ptravnik/Retro_CALC/HWKbd/src/Cyrillic_Phonetic_CP1251.h

/*
  Cyrillic_Phonetic_CP1251.h - codes and macros for Hardware keyboard.
  Copyright (c) 2019 Pavel Travnik.  All rights reserved.

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
  You should have received a copy of the GNU Lesser General Public
  License along with this library; if not, write to the Free Software
  Foundation, Inc., 51 Franklin St, Fifth Floor, Boston, MA  02110-1301  USA
*/
const static uint16_t HWKBD_Codepage_Cyrillic_Phonetic_CP1251[] PROGMEM = {
  0x001b, 0x001b, 0x2009, 0x3009, 0x401b, 0x401b, 0x6009, 0x7009, // Button 01
  0x8000, 0x002b, 0x8003, 0x8009, 0x40fd, 0x40dd, 0xc00f, 0x402b, // Button 02
  0x8015, 0x002d, 0x8018, 0x002d, 0x40fe, 0x40de, 0xc01e, 0x402d, // Button 03
  0x8024, 0x002a, 0x8027, 0x002a, 0x40fa, 0x40da, 0xc02e, 0x402a, // Button 04
  0x8035, 0x002f, 0x8038, 0x803f, 0x40fc, 0x40dc, 0xc045, 0x402f, // Button 05
  0x804c, 0x005e, 0x005e, 0x804f, 0x40b8, 0x40a8, 0x405e, 0x405e, // Button 06
  0x8056, 0x007e, 0x005c, 0x8059, 0x407e, 0x405c, 0x40b1, 0x40b1, // Button 07
  0x0065, 0x0065, 0x0065, 0x0065, 0x40f8, 0x40d8, 0x4065, 0x4065, // Button 08
  0x002e, 0x002c, 0x003a, 0x003b, 0x40f9, 0x40d9, 0x40b0, 0x403b, // Button 09
  0x805f, 0x8065, 0x806c, 0xb074, 0xc07b, 0xc081, 0xc088, 0xf090, // Button 10
  0x0031, 0x0021, 0x0000, 0x0000, 0x4031, 0x4021, 0x4000, 0x4000, // Button 11
  0x0032, 0x0040, 0x0000, 0x0000, 0x4032, 0x4040, 0x4000, 0x4000, // Button 12
  0x0033, 0x0023, 0x0000, 0x0000, 0x4033, 0x4023, 0x4000, 0x4000, // Button 13
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
  0x32, 0x0d, 0x00, 0x0a, 0x72, 0x61, 0x64, 0x69,
  0x75, 0x73, 0x0d, 0x00, 0x0a, 0x63, 0x61, 0x74,
  0x68, 0x0d, 0x00, 0x0a, 0x72, 0x61, 0x64, 0x69,
  0x75, 0x73, 0x0d, 0x00, 0x0a, 0x63, 0x61, 0x74,
  0x68, 0x0d, 0x00, 0x0a, 0x63, 0x6c, 0x65, 0x61,
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
};
