ptravnik/Retro_CALC/RetroRPN_ESP32/src/Keywords.cpp

//////////////////////////////////////////////////////////
//
//  RetroRPN - "Электроника МК-90" reborn
//  Copyright (c) 2019 Pavel Travnik.  All rights reserved.
//  See main file for the license
//
//////////////////////////////////////////////////////////

#include "Keywords.hpp"

//#define __DEBUG

//#define _OPR_ABS_KW             0
const char _OPR_ABS[] PROGMEM = "ABS";
const char _OPR_abs[] PROGMEM = "abs";
//#define _OPR_ACOS_KW            1
const char _OPR_ACOS[] PROGMEM = "ACOS";
const char _OPR_acos[] PROGMEM = "acos";
//#define _OPR_ACOSH_KW           2
const char _OPR_ACOSH[] PROGMEM = "ACOSH";
const char _OPR_acosh[] PROGMEM = "acosh";
//#define _OPR_ADD_KW             3
const char _OPR_ADD[] PROGMEM = "ADD";
const char _OPR_add[] PROGMEM = "add";
//#define _OPR_AMODE_KW           4
const char _OPR_AMODE[] PROGMEM = "AMODE";
const char _OPR_amode[] PROGMEM = "amode";
//#define _OPR_API2GCC_KW         5
const char _OPR_API2GCC[] PROGMEM = "API2GCC";
const char _OPR_api2gcc[] PROGMEM = "api2gcc";
//#define _OPR_APPEND_KW          6
const char _OPR_APPEND[] PROGMEM = "APPEND";
const char _OPR_append[] PROGMEM = "append";
//#define _OPR_AREAD_KW           7
const char _OPR_AREAD[] PROGMEM = "AREAD";
const char _OPR_aread[] PROGMEM = "aread";
//#define _OPR_AREAD_INT_KW       8
const char _OPR_AREAD_INT[] PROGMEM = "AREAD%";
const char _OPR_aread_INT[] PROGMEM = "aread%";
//#define _OPR_ASC_KW             9
const char _OPR_ASC[] PROGMEM = "ASC";
const char _OPR_asc[] PROGMEM = "asc";
//#define _OPR_ASIN_KW            10
const char _OPR_ASIN[] PROGMEM = "ASIN";
const char _OPR_asin[] PROGMEM = "asin";
//#define _OPR_ASINH_KW           11
const char _OPR_ASINH[] PROGMEM = "ASINH";
const char _OPR_asinh[] PROGMEM = "asinh";
//#define _OPR_AT_KW              12
const char _OPR_AT[] PROGMEM = "AT";
const char _OPR_at[] PROGMEM = "at";
//#define _OPR_ATAN_KW            13
const char _OPR_ATAN[] PROGMEM = "ATAN";
const char _OPR_atan[] PROGMEM = "atan";
//#define _OPR_ATANH_KW           14
const char _OPR_ATANH[] PROGMEM = "ATANH";
const char _OPR_atanh[] PROGMEM = "atanh";
//#define _OPR_AWRITE_KW          15
const char _OPR_AWRITE[] PROGMEM = "AWRITE";
const char _OPR_awrite[] PROGMEM = "awrite";
//#define _OPR_AZIMUTH_KW         16
const char _OPR_AZIMUTH[] PROGMEM = "AZIMUTH";
const char _OPR_azimuth[] PROGMEM = "azimuth";
//#define _OPR_AZIMUTH3_KW        17
const char _OPR_AZIMUTH3[] PROGMEM = "AZIMUTH3";
const char _OPR_azimuth3[] PROGMEM = "azimuth3";
//#define _OPR_BAR2PSI_KW         18
const char _OPR_BAR2PSI[] PROGMEM = "BAR2PSI";
const char _OPR_bar2psi[] PROGMEM = "bar2psi";
//#define _OPR_BBL2CM_KW          19
const char _OPR_BBL2CM[] PROGMEM = "BBL2CM";
const char _OPR_bbl2cm[] PROGMEM = "bbl2cm";
//#define _OPR_BREAK_KW           20
const char _OPR_BREAK[] PROGMEM = "BREAK";
const char _OPR_break[] PROGMEM = "break";
//#define _OPR_C2F_KW             21
const char _OPR_C2F[] PROGMEM = "C2F";
const char _OPR_c2f[] PROGMEM = "c2f";
//#define _OPR_C2K_KW             22
const char _OPR_C2K[] PROGMEM = "C2K";
const char _OPR_c2k[] PROGMEM = "c2k";
//#define _OPR_CATH_KW            23
const char _OPR_CATH[] PROGMEM = "CATH";
const char _OPR_cath[] PROGMEM = "cath";
//#define _OPR_CF2CM_KW           24
const char _OPR_CF2CM[] PROGMEM = "CF2CM";
const char _OPR_cf2cm[] PROGMEM = "cf2cm";
//#define _OPR_CHAIN_KW           25
const char _OPR_CHAIN[] PROGMEM = "CHAIN";
const char _OPR_chain[] PROGMEM = "chain";
//#define _OPR_CHR_STR_KW         26
const char _OPR_CHR_STR[] PROGMEM = "CHR$";
const char _OPR_chr_STR[] PROGMEM = "chr$";
//#define _OPR_CIRCLE_KW          27
const char _OPR_CIRCLE[] PROGMEM = "CIRCLE";
const char _OPR_circle[] PROGMEM = "circle";
//#define _OPR_CLEAR_KW           28
const char _OPR_CLEAR[] PROGMEM = "CLEAR";
const char _OPR_clear[] PROGMEM = "clear";
//#define _OPR_CLI_KW             29
const char _OPR_CLI[] PROGMEM = "CLI";
const char _OPR_cli[] PROGMEM = "cli";
//#define _OPR_CLOSE_KW           30
const char _OPR_CLOSE[] PROGMEM = "CLOSE";
const char _OPR_close[] PROGMEM = "close";
//#define _OPR_CLS_KW             31
const char _OPR_CLS[] PROGMEM = "CLS";
const char _OPR_cls[] PROGMEM = "cls";
//#define _OPR_CM2BBL_KW          32
const char _OPR_CM2BBL[] PROGMEM = "CM2BBL";
const char _OPR_cm2bbl[] PROGMEM = "cm2bbl";
//#define _OPR_CM2CF_KW           33
const char _OPR_CM2CF[] PROGMEM = "CM2CF";
const char _OPR_cm2cf[] PROGMEM = "cm2cf";
//#define _OPR_COLOR_KW           34
const char _OPR_COLOR[] PROGMEM = "COLOR";
const char _OPR_color[] PROGMEM = "color";
//#define _OPR_CON_KW             35
const char _OPR_CON[] PROGMEM = "CON";
const char _OPR_con[] PROGMEM = "con";
//#define _OPR_CONST_KW           36
const char _OPR_CONST[] PROGMEM = "CONST";
const char _OPR_const[] PROGMEM = "const";
//#define _OPR_CONT_KW            37
const char _OPR_CONT[] PROGMEM = "CONT";
const char _OPR_cont[] PROGMEM = "cont";
//#define _OPR_CONTINUE_KW        38
const char _OPR_CONTINUE[] PROGMEM = "CONTINUE";
const char _OPR_continue[] PROGMEM = "continue";
//#define _OPR_COORDS_KW          39
const char _OPR_COORDS[] PROGMEM = "COORDS";
const char _OPR_coords[] PROGMEM = "coords";
//#define _OPR_COORDS3_KW         40
const char _OPR_COORDS3[] PROGMEM = "COORDS3";
const char _OPR_coords3[] PROGMEM = "coords3";
//#define _OPR_COS_KW             41
const char _OPR_COS[] PROGMEM = "COS";
const char _OPR_cos[] PROGMEM = "cos";
//#define _OPR_COSH_KW            42
const char _OPR_COSH[] PROGMEM = "COSH";
const char _OPR_cosh[] PROGMEM = "cosh";
//#define _OPR_COT_KW             43
const char _OPR_COT[] PROGMEM = "COT";
const char _OPR_cot[] PROGMEM = "cot";
//#define _OPR_CURSOR_KW          44
const char _OPR_CURSOR[] PROGMEM = "CURSOR";
const char _OPR_cursor[] PROGMEM = "cursor";
//#define _OPR_D2DMS_KW           45
const char _OPR_D2DMS[] PROGMEM = "D2DMS";
const char _OPR_d2dms[] PROGMEM = "d2dms";
//#define _OPR_DATA_KW            46
const char _OPR_DATA[] PROGMEM = "DATA";
const char _OPR_data[] PROGMEM = "data";
//#define _OPR_DEF_KW             47
const char _OPR_DEF[] PROGMEM = "DEF";
const char _OPR_def[] PROGMEM = "def";
//#define _OPR_DELAY_KW           48
const char _OPR_DELAY[] PROGMEM = "DELAY";
const char _OPR_delay[] PROGMEM = "delay";
//#define _OPR_DET_KW             49
const char _OPR_DET[] PROGMEM = "DET";
const char _OPR_det[] PROGMEM = "det";
//#define _OPR_DIM_KW             50
const char _OPR_DIM[] PROGMEM = "DIM";
const char _OPR_dim[] PROGMEM = "dim";
//#define _OPR_DIR_KW             51
const char _OPR_DIR[] PROGMEM = "DIR";
const char _OPR_dir[] PROGMEM = "dir";
//#define _OPR_DIRECTORY_KW       52
const char _OPR_DIRECTORY[] PROGMEM = "CD";
const char _OPR_directory[] PROGMEM = "cd";
//#define _OPR_DIV_KW             53
const char _OPR_DIV[] PROGMEM = "DIV";
const char _OPR_div[] PROGMEM = "div";
//#define _OPR_DMODE_KW           54
const char _OPR_DMODE[] PROGMEM = "DMODE";
const char _OPR_dmode[] PROGMEM = "dmode";
//#define _OPR_DMS2D_KW           55
const char _OPR_DMS2D[] PROGMEM = "DMS2D";
const char _OPR_dms2d[] PROGMEM = "dms2d";
//#define _OPR_DNOTONE_KW         56
const char _OPR_DNOTONE[] PROGMEM = "DNOTONE";
const char _OPR_dnotone[] PROGMEM = "dnotone";
//#define _OPR_DOT_KW             57
const char _OPR_DOT[] PROGMEM = "DOT";
const char _OPR_dot[] PROGMEM = "dot";
//#define _OPR_DREAD_KW           58
const char _OPR_DREAD[] PROGMEM = "DREAD";
const char _OPR_dread[] PROGMEM = "dread";
//#define _OPR_DTONE_KW           59
const char _OPR_DTONE[] PROGMEM = "DTONE";
const char _OPR_dtone[] PROGMEM = "dtone";
//#define _OPR_DUMP_KW            60
const char _OPR_DUMP[] PROGMEM = "DUMP";
const char _OPR_dump[] PROGMEM = "dump";
//#define _OPR_DWRITE_KW          61
const char _OPR_DWRITE[] PROGMEM = "DWRITE";
const char _OPR_dwrite[] PROGMEM = "dwrite";
//#define _OPR_EDIT_KW            62
const char _OPR_EDIT[] PROGMEM = "EDIT";
const char _OPR_edit[] PROGMEM = "edit";
//#define _OPR_ELLIPSE_KW         63
const char _OPR_ELLIPSE[] PROGMEM = "ELLIPSE";
const char _OPR_ellipse[] PROGMEM = "ellipse";
//#define _OPR_ELSE_KW            64
const char _OPR_ELSE[] PROGMEM = "ELSE";
const char _OPR_else[] PROGMEM = "else";
//#define _OPR_END_KW             65
const char _OPR_END[] PROGMEM = "END";
const char _OPR_end[] PROGMEM = "end";
//#define _OPR_ENDIF_KW           66
const char _OPR_ENDIF[] PROGMEM = "ENDIF";
const char _OPR_endif[] PROGMEM = "endif";
//#define _OPR_ENDLOOP_KW         67
const char _OPR_ENDLOOP[] PROGMEM = "ENDLOOP";
const char _OPR_endloop[] PROGMEM = "endloop";
//#define _OPR_EXP_KW             68
const char _OPR_EXP[] PROGMEM = "EXP";
const char _OPR_exp[] PROGMEM = "exp";
//#define _OPR_F2C_KW             69
const char _OPR_F2C[] PROGMEM = "F2C";
const char _OPR_f2c[] PROGMEM = "f2c";
//#define _OPR_FLOAT_KW           70
const char _OPR_FLOAT[] PROGMEM = "FLOAT";
const char _OPR_float[] PROGMEM = "float";
//#define _OPR_FMAN_KW            71
const char _OPR_FMAN[] PROGMEM = "FMAN";
const char _OPR_fman[] PROGMEM = "fman";
//#define _OPR_FN_KW              72
const char _OPR_FN[] PROGMEM = "FN";
const char _OPR_fn[] PROGMEM = "fn";
//#define _OPR_FOR_KW             73
const char _OPR_FOR[] PROGMEM = "FOR";
const char _OPR_for[] PROGMEM = "for";
//#define _OPR_FREAD_KW           74
const char _OPR_FREAD[] PROGMEM = "FREAD";
const char _OPR_fread[] PROGMEM = "fread";
//#define _OPR_FREAD_STR_KW       75
const char _OPR_FREAD_STR[] PROGMEM = "FREAD$";
const char _OPR_fread_STR[] PROGMEM = "fread$";
//#define _OPR_FSIZE_KW           76
const char _OPR_FSIZE[] PROGMEM = "FSIZE";
const char _OPR_fsize[] PROGMEM = "fsize";
//#define _OPR_FT2M_KW            77
const char _OPR_FT2M[] PROGMEM = "FT2M";
const char _OPR_ft2m[] PROGMEM = "ft2m";
//#define _OPR_GAL2L_KW           78
const char _OPR_GAL2L[] PROGMEM = "GAL2L";
const char _OPR_gal2l[] PROGMEM = "gal2l";
//#define _OPR_GCC2API_KW         79
const char _OPR_GCC2API[] PROGMEM = "GCC2API";
const char _OPR_gcc2api[] PROGMEM = "gcc2api";
//#define _OPR_GOFF2_KW           80
const char _OPR_GOFF2[] PROGMEM = "GOFF2";
const char _OPR_goff2[] PROGMEM = "goff2";
//#define _OPR_GOSUB_KW           81
const char _OPR_GOSUB[] PROGMEM = "GOSUB";
const char _OPR_gosub[] PROGMEM = "gosub";
//#define _OPR_GOTO_KW            82
const char _OPR_GOTO[] PROGMEM = "GOTO";
const char _OPR_goto[] PROGMEM = "goto";
//#define _OPR_HEX_STR_KW         83
const char _OPR_HEX_STR[] PROGMEM = "HEX$";
const char _OPR_hex_STR[] PROGMEM = "hex$";
//#define _OPR_IDN_KW             84
const char _OPR_IDN[] PROGMEM = "IDN";
const char _OPR_idn[] PROGMEM = "idn";
//#define _OPR_IF_KW              85
const char _OPR_IF[] PROGMEM = "IF";
const char _OPR_if[] PROGMEM = "if";
//#define _OPR_INCH16_STR_KW      86
const char _OPR_INCH16_STR[] PROGMEM = "INCH16$";
const char _OPR_inch16_STR[] PROGMEM = "inch16$";
//#define _OPR_INCH2_STR_KW       87
const char _OPR_INCH2_STR[] PROGMEM = "INCH2$";
const char _OPR_inch2_STR[] PROGMEM = "inch2$";
//#define _OPR_INCH32_STR_KW      88
const char _OPR_INCH32_STR[] PROGMEM = "INCH32$";
const char _OPR_inch32_STR[] PROGMEM = "inch32$";
//#define _OPR_INCH32_STR_KW      89
const char _OPR_INCH64_STR[] PROGMEM = "INCH64$";
const char _OPR_inch64_STR[] PROGMEM = "inch64$";
//#define _OPR_INCH4_STR_KW       90
const char _OPR_INCH4_STR[] PROGMEM = "INCH4$";
const char _OPR_inch4_STR[] PROGMEM = "inch4$";
//#define _OPR_INCH8_STR_KW       91
const char _OPR_INCH8_STR[] PROGMEM = "INCH8$";
const char _OPR_inch8_STR[] PROGMEM = "inch8$";
//#define _OPR_INJ_KW             92
const char _OPR_INJ[] PROGMEM = "INJ";
const char _OPR_inj[] PROGMEM = "inj";
//#define _OPR_INKEY_STR_KW       93
const char _OPR_INKEY_STR[] PROGMEM = "INKEY$";
const char _OPR_inkey_STR[] PROGMEM = "inkey$";
//#define _OPR_INPUT_KW           94
const char _OPR_INPUT[] PROGMEM = "INPUT";
const char _OPR_input[] PROGMEM = "input";
//#define _OPR_INSCAN_STR_KW      95
const char _OPR_INSCAN_STR[] PROGMEM = "INSCAN$";
const char _OPR_inscan_STR[] PROGMEM = "inscan$";
//#define _OPR_INT_INT_KW         96
const char _OPR_INT_INT[] PROGMEM = "INT%";
const char _OPR_int_INT[] PROGMEM = "int%";
//#define _OPR_INV_KW             97
const char _OPR_INV[] PROGMEM = "INV";
const char _OPR_inv[] PROGMEM = "inv";
//#define _OPR_KG2LBS_KW          98
const char _OPR_KG2LBS[] PROGMEM = "KG2LBS";
const char _OPR_kg2lbs[] PROGMEM = "kg2lbs";
//#define _OPR_KM2M_KW            99
const char _OPR_KM2M[] PROGMEM = "KM2M";
const char _OPR_km2m[] PROGMEM = "km2m";
//#define _OPR_KM2NM_KW           100
const char _OPR_KM2NM[] PROGMEM = "KM2NM";
const char _OPR_km2nm[] PROGMEM = "km2nm";
//#define _OPR_KMH2MS_KW          101
const char _OPR_KMH2MS[] PROGMEM = "KMH2MS";
const char _OPR_kmh2ms[] PROGMEM = "kmh2ms";
//#define _OPR_L2GAL_KW           102
const char _OPR_L2GAL[] PROGMEM = "L2GAL";
const char _OPR_l2gal[] PROGMEM = "l2gal";
//#define _OPR_LBS2KG_KW          103
const char _OPR_LBS2KG[] PROGMEM = "LBS2KG";
const char _OPR_lbs2kg[] PROGMEM = "lbs2kg";
//#define _OPR_LCIRC_KW           104
const char _OPR_LCIRC[] PROGMEM = "LCIRC";
const char _OPR_lcirc[] PROGMEM = "lcirc";
//#define _OPR_LEFT_STR_KW        105
const char _OPR_LEFT_STR[] PROGMEM = "LEFT$";
const char _OPR_left_STR[] PROGMEM = "left$";
//#define _OPR_LET_KW             106
const char _OPR_LET[] PROGMEM = "LET";
const char _OPR_let[] PROGMEM = "let";
//#define _OPR_LG_KW              107
const char _OPR_LG[] PROGMEM = "LG";
const char _OPR_lg[] PROGMEM = "lg";
//#define _OPR_LIN2_KW            108
const char _OPR_LIN2[] PROGMEM = "LIN2";
const char _OPR_lin2[] PROGMEM = "lin2";
//#define _OPR_LINE_KW            109
const char _OPR_LINE[] PROGMEM = "LINE";
const char _OPR_line[] PROGMEM = "line";
//#define _OPR_LINETO_KW          110
const char _OPR_LINETO[] PROGMEM = "LINETO";
const char _OPR_lineto[] PROGMEM = "lineto";
//#define _OPR_LINEW_KW           111
const char _OPR_LINEW[] PROGMEM = "LINEW";
const char _OPR_linew[] PROGMEM = "linew";
//#define _OPR_LIST_KW            112
const char _OPR_LIST[] PROGMEM = "LIST";
const char _OPR_list[] PROGMEM = "list";
//#define _OPR_LN_KW              113
const char _OPR_LN[] PROGMEM = "LN";
const char _OPR_ln[] PROGMEM = "ln";
//#define _OPR_LOAD_KW            114
const char _OPR_LOAD[] PROGMEM = "LOAD";
const char _OPR_load[] PROGMEM = "load";
//#define _OPR_LOG_KW             115
const char _OPR_LOG[] PROGMEM = "LOG";
const char _OPR_log[] PROGMEM = "log";
//#define _OPR_LOOP_KW            116
const char _OPR_LOOP[] PROGMEM = "LOOP";
const char _OPR_loop[] PROGMEM = "loop";
//#define _OPR_LT2MT_KW           117
const char _OPR_LT2MT[] PROGMEM = "LT2MT";
const char _OPR_lt2mt[] PROGMEM = "lt2mt";
//#define _OPR_M2FT_KW            118
const char _OPR_M2FT[] PROGMEM = "M2FT";
const char _OPR_m2ft[] PROGMEM = "m2ft";
//#define _OPR_M2KM_KW            119
const char _OPR_M2KM[] PROGMEM = "M2KM";
const char _OPR_m2km[] PROGMEM = "m2km";
//#define _OPR_MAT_KW             120
const char _OPR_MAT[] PROGMEM = "MAT";
const char _OPR_mat[] PROGMEM = "mat";
//#define _OPR_MATRIX_KW          121
const char _OPR_MATRIX[] PROGMEM = "MATRIX";
const char _OPR_matrix[] PROGMEM = "matrix";
//#define _OPR_MEM_KW             122
const char _OPR_MEM[] PROGMEM = "MEM";
const char _OPR_mem[] PROGMEM = "mem";
//#define _OPR_MID_STR_KW         123
const char _OPR_MID_STR[] PROGMEM = "MID$";
const char _OPR_mid_STR[] PROGMEM = "mid$";
//#define _OPR_MM2IN_KW           124
const char _OPR_MM2IN[] PROGMEM = "MM2IN";
const char _OPR_mm2in[] PROGMEM = "mm2in";
//#define _OPR_MOD_KW             125
const char _OPR_MOD[] PROGMEM = "MOD";
const char _OPR_mod[] PROGMEM = "mod";
//#define _OPR_MPA2PSI_KW         126
const char _OPR_MPA2PSI[] PROGMEM = "MPA2PSI";
const char _OPR_mpa2psi[] PROGMEM = "mpa2psi";
//#define _OPR_MS2KMH_KW          127
const char _OPR_MS2KMH[] PROGMEM = "MS2KMH";
const char _OPR_ms2kmh[] PROGMEM = "ms2kmh";
//#define _OPR_MT2LT_KW           128
const char _OPR_MT2LT[] PROGMEM = "MT2LT";
const char _OPR_mt2lt[] PROGMEM = "mt2lt";
//#define _OPR_MT2ST_KW           129
const char _OPR_MT2ST[] PROGMEM = "MT2ST";
const char _OPR_mt2st[] PROGMEM = "mt2st";
//#define _OPR_MUL_KW             130
const char _OPR_MUL[] PROGMEM = "MUL";
const char _OPR_mul[] PROGMEM = "mul";
//#define _OPR_NDIS_KW            131
const char _OPR_NDIS[] PROGMEM = "NDIS";
const char _OPR_ndis[] PROGMEM = "ndis";
//#define _OPR_NEG_KW             132
const char _OPR_NEG[] PROGMEM = "NEG";
const char _OPR_neg[] PROGMEM = "neg";
//#define _OPR_NEW_KW             133
const char _OPR_NEW[] PROGMEM = "NEW";
const char _OPR_new[] PROGMEM = "new";
//#define _OPR_NEXT_KW            134
const char _OPR_NEXT[] PROGMEM = "NEXT";
const char _OPR_next[] PROGMEM = "next";
//#define _OPR_NM2KM_KW           135
const char _OPR_NM2KM[] PROGMEM = "NM2KM";
const char _OPR_nm2km[] PROGMEM = "nm2km";
//#define _OPR_OPEN_KW            136
const char _OPR_OPEN[] PROGMEM = "OPEN";
const char _OPR_open[] PROGMEM = "open";
//#define _OPR_PA2PSI_KW          137
const char _OPR_PA2PSI[] PROGMEM = "PA2PSI";
const char _OPR_pa2psi[] PROGMEM = "pa2psi";
//#define _OPR_PAUSE_KW           138
const char _OPR_PAUSE[] PROGMEM = "PAUSE";
const char _OPR_pause[] PROGMEM = "pause";
//#define _OPR_POINT_KW           139
const char _OPR_POINT[] PROGMEM = "POINT";
const char _OPR_point[] PROGMEM = "point";
//#define _OPR_POKE_KW            140
const char _OPR_POKE[] PROGMEM = "POKE";
const char _OPR_poke[] PROGMEM = "poke";
//#define _OPR_POP_KW             141
const char _OPR_POP[] PROGMEM = "POP";
const char _OPR_pop[] PROGMEM = "pop";
//#define _OPR_POW_KW             142
const char _OPR_POW[] PROGMEM = "POW";
const char _OPR_pow[] PROGMEM = "pow";
//#define _OPR_PRINT_KW           143
const char _OPR_PRINT[] PROGMEM = "PRINT";
const char _OPR_print[] PROGMEM = "print";
//#define _OPR_PRINTALT_KW        144
const char _OPR_PRINTALT[] PROGMEM = "?";
const char _OPR_printalt[] PROGMEM = "?";
//#define _OPR_PROB_KW            145
const char _OPR_PROB[] PROGMEM = "PROB";
const char _OPR_prob[] PROGMEM = "prob";
//#define _OPR_PROBIT_KW          146
const char _OPR_PROBIT[] PROGMEM = "PROBIT";
const char _OPR_probit[] PROGMEM = "probit";
//#define _OPR_PROBR_KW           147
const char _OPR_PROBR[] PROGMEM = "PROBR";
const char _OPR_probr[] PROGMEM = "probr";
//#define _OPR_PROGRAM_KW         148
const char _OPR_PROGRAM[] PROGMEM = "PROGRAM";
const char _OPR_program[] PROGMEM = "program";
//#define _OPR_PSI2BAR_KW         149
const char _OPR_PSI2BAR[] PROGMEM = "PSI2BAR";
const char _OPR_psi2bar[] PROGMEM = "psi2bar";
//#define _OPR_PSI2MPA_KW         150
const char _OPR_PSI2MPA[] PROGMEM = "PSI2MPA";
const char _OPR_psi2mpa[] PROGMEM = "psi2mpa";
//#define _OPR_PSI2PA_KW          151
const char _OPR_PSI2PA[] PROGMEM = "PSI2PA";
const char _OPR_psi2pa[] PROGMEM = "psi2pa";
//#define _OPR_PSIA2PSIG_KW       152
const char _OPR_PSIA2PSIG[] PROGMEM = "PSIA2PSIG";
const char _OPR_psia2psig[] PROGMEM = "psia2psig";
//#define _OPR_PSIG2PSIA_KW       153
const char _OPR_PSIG2PSIA[] PROGMEM = "PSIG2PSIA";
const char _OPR_psig2psia[] PROGMEM = "psig2psia";
//#define _OPR_PUSH_KW            154
const char _OPR_PUSH[] PROGMEM = "PUSH";
const char _OPR_push[] PROGMEM = "push";
//#define _OPR_QUAD_KW            155
const char _OPR_QUAD[] PROGMEM = "QUAD";
const char _OPR_quad[] PROGMEM = "quad";
//#define _OPR_RADIUS_KW          156
const char _OPR_RADIUS[] PROGMEM = "RADIUS";
const char _OPR_radius[] PROGMEM = "radius";
//#define _OPR_RANDOM_KW          157
const char _OPR_RANDOM[] PROGMEM = "RANDOM";
const char _OPR_random[] PROGMEM = "random";
//#define _OPR_RANDOM_INT_KW      158
const char _OPR_RANDOM_INT[] PROGMEM = "RANDOM%";
const char _OPR_random_INT[] PROGMEM = "random%";
//#define _OPR_READ_KW            159
const char _OPR_READ[] PROGMEM = "READ";
const char _OPR_read[] PROGMEM = "read";
//#define _OPR_RECT_KW            160
const char _OPR_RECT[] PROGMEM = "RECT";
const char _OPR_rect[] PROGMEM = "rect";
//#define _OPR_REGR_KW            161
const char _OPR_REGR[] PROGMEM = "REGR";
const char _OPR_regr[] PROGMEM = "regr";
//#define _OPR_REM_KW             162
const char _OPR_REM[] PROGMEM = "REM";
const char _OPR_rem[] PROGMEM = "rem";
//#define _OPR_REMALT_KW          163
const char _OPR_REMALT[] PROGMEM = "#";
const char _OPR_remalt[] PROGMEM = "#";
//#define _OPR_RESET_KW           164
const char _OPR_RESET[] PROGMEM = "RESET";
const char _OPR_reset[] PROGMEM = "reset";
//#define _OPR_RESTORE_KW         165
const char _OPR_RESTORE[] PROGMEM = "RESTORE";
const char _OPR_restore[] PROGMEM = "restore";
//#define _OPR_RIGHT_STR_KW       166
const char _OPR_RIGHT_STR[] PROGMEM = "RIGHT$";
const char _OPR_right_STR[] PROGMEM = "right$";
//#define _OPR_RMD_KW             167
const char _OPR_RMD[] PROGMEM = "RMD";
const char _OPR_rmd[] PROGMEM = "rmd";
//#define _OPR_RND_KW             168
const char _OPR_RND[] PROGMEM = "RND";
const char _OPR_rnd[] PROGMEM = "rnd";
//#define _OPR_ROOT_KW            169
const char _OPR_ROOT[] PROGMEM = "ROOT";
const char _OPR_root[] PROGMEM = "root";
//#define _OPR_ROT_KW             170
const char _OPR_ROT[] PROGMEM = "ROT";
const char _OPR_rot[] PROGMEM = "rot";
//#define _OPR_ROT3c_KW           171
const char _OPR_ROT3c[] PROGMEM = "ROT3c";
const char _OPR_rot3c[] PROGMEM = "rot3c";
//#define _OPR_ROT3s_KW           172
const char _OPR_ROT3s[] PROGMEM = "ROT3s";
const char _OPR_rot3s[] PROGMEM = "rot3s";
//#define _OPR_ROUND_KW           173
const char _OPR_ROUND[] PROGMEM = "ROUND";
const char _OPR_round[] PROGMEM = "round";
//#define _OPR_RPN_KW             174
const char _OPR_RPN[] PROGMEM = "RPN";
const char _OPR_rpn[] PROGMEM = "rpn";
//#define _OPR_RUN_KW             175
const char _OPR_RUN[] PROGMEM = "RUN";
const char _OPR_run[] PROGMEM = "run";
//#define _OPR_SAVE_KW            176
const char _OPR_SAVE[] PROGMEM = "SAVE";
const char _OPR_save[] PROGMEM = "save";
//#define _OPR_SCIRC_KW           177
const char _OPR_SCIRC[] PROGMEM = "SCIRC";
const char _OPR_scirc[] PROGMEM = "scirc";
//#define _OPR_SCREEN_KW          178
const char _OPR_SCREEN[] PROGMEM = "SCREEN";
const char _OPR_screen[] PROGMEM = "screen";
//#define _OPR_SEED_KW            179
const char _OPR_SEED[] PROGMEM = "SEED";
const char _OPR_seed[] PROGMEM = "seed";
//#define _OPR_SIGN_KW            180
const char _OPR_SIGN[] PROGMEM = "SIGN";
const char _OPR_sign[] PROGMEM = "sign";
//#define _OPR_SIN_KW             181
const char _OPR_SIN[] PROGMEM = "SIN";
const char _OPR_sin[] PROGMEM = "sin";
//#define _OPR_SINH_KW            182
const char _OPR_SINH[] PROGMEM = "SINH";
const char _OPR_sinh[] PROGMEM = "sinh";
//#define _OPR_SM2SFT_KW          183
const char _OPR_SM2SFT[] PROGMEM = "SM2SFT";
const char _OPR_sm2sft[] PROGMEM = "sm2sft";
//#define _OPR_SQ_KW              184
const char _OPR_SQ[] PROGMEM = "SQ";
const char _OPR_sq[] PROGMEM = "sq";
//#define _OPR_SQRT_KW            185
const char _OPR_SQRT[] PROGMEM = "SQRT";
const char _OPR_sqrt[] PROGMEM = "sqrt";
//#define _OPR_SSPHERE_KW         186
const char _OPR_SSPHERE[] PROGMEM = "SSPHERE";
const char _OPR_ssphere[] PROGMEM = "ssphere";
//#define _OPR_ST2MT_KW           187
const char _OPR_ST2MT[] PROGMEM = "ST2MT";
const char _OPR_st2mt[] PROGMEM = "st2mt";
//#define _OPR_STACK_KW           188
const char _OPR_STACK[] PROGMEM = "STACK";
const char _OPR_stack[] PROGMEM = "stack";
//#define _OPR_STAT_KW            189
const char _OPR_STAT[] PROGMEM = "STAT";
const char _OPR_stat[] PROGMEM = "stat";
//#define _OPR_STATXY_KW          190
const char _OPR_STATXY[] PROGMEM = "STATXY";
const char _OPR_statxy[] PROGMEM = "statxy";
//#define _OPR_STEP_KW            191
const char _OPR_STEP[] PROGMEM = "STEP";
const char _OPR_step[] PROGMEM = "step";
//#define _OPR_STOP_KW            192
const char _OPR_STOP[] PROGMEM = "STOP";
const char _OPR_stop[] PROGMEM = "stop";
//#define _OPR_STORE_KW           193
const char _OPR_STORE[] PROGMEM = "STORE";
const char _OPR_store[] PROGMEM = "store";
//#define _OPR_STR_STR_KW         194
const char _OPR_STR_STR[] PROGMEM = "STR$";
const char _OPR_str_STR[] PROGMEM = "str$";
//#define _OPR_SUB_KW             195
const char _OPR_SUB[] PROGMEM = "SUB";
const char _OPR_sub[] PROGMEM = "sub";
//#define _OPR_SUM_KW             196
const char _OPR_SUM[] PROGMEM = "SUM";
const char _OPR_sum[] PROGMEM = "sum";
//#define _OPR_SUMS_KW            197
const char _OPR_SUMS[] PROGMEM = "SUMS";
const char _OPR_sums[] PROGMEM = "sums";
//#define _OPR_SUMXY_KW           198
const char _OPR_SUMXY[] PROGMEM = "SUMXY";
const char _OPR_sumxy[] PROGMEM = "sumxy";
//#define _OPR_SWAP_KW            199
const char _OPR_SWAP[] PROGMEM = "SWAP";
const char _OPR_swap[] PROGMEM = "swap";
//#define _OPR_TAN_KW             200
const char _OPR_TAN[] PROGMEM = "TAN";
const char _OPR_tan[] PROGMEM = "tan";
//#define _OPR_TANH_KW            201
const char _OPR_TANH[] PROGMEM = "TANH";
const char _OPR_tanh[] PROGMEM = "tanh";
//#define _OPR_TERM_KW            202
const char _OPR_TERM[] PROGMEM = "TERM";
const char _OPR_term[] PROGMEM = "term";
//#define _OPR_TIME_KW            203
const char _OPR_TIME[] PROGMEM = "TIME";
const char _OPR_time[] PROGMEM = "time";
//#define _OPR_TO_KW              204
const char _OPR_TO[] PROGMEM = "TO";
const char _OPR_to[] PROGMEM = "to";
//#define _OPR_TRN_KW             205
const char _OPR_TRN[] PROGMEM = "TRN";
const char _OPR_trn[] PROGMEM = "trn";
//#define _OPR_VARS_KW            206
const char _OPR_VARS[] PROGMEM = "VARS";
const char _OPR_vars[] PROGMEM = "vars";
//#define _OPR_VECTOR_KW          207
const char _OPR_VECTOR[] PROGMEM = "VECTOR";
const char _OPR_vector[] PROGMEM = "vector";
//#define _OPR_VSPHERE_KW         208
const char _OPR_VSPHERE[] PROGMEM = "VSPHERE";
const char _OPR_vsphere[] PROGMEM = "vsphere";
//#define _OPR_WEEKDAY_KW         209
const char _OPR_WEEKDAY[] PROGMEM = "WEEKDAY";
const char _OPR_weekday[] PROGMEM = "weekday";
//#define _OPR_WRITE_KW           210
const char _OPR_WRITE[] PROGMEM = "WRITE";
const char _OPR_write[] PROGMEM = "write";
//#define _OPR_ZER_KW             211
const char _OPR_ZER[] PROGMEM = "ZER";
const char _OPR_zer[] PROGMEM = "zer";
//#define _OPR_ROLL_KW            212
const char _OPR_ROLL[] PROGMEM = "ROLL";
const char _OPR_roll[] PROGMEM = "roll";
//#define _OPR_OOX_KW             213
const char _OPR_OOX[] PROGMEM = "OOX";
const char _OPR_oox[] PROGMEM = "oox";
//#define _OPR_FACT_KW             214
const char _OPR_FACT[] PROGMEM = "FACT";
const char _OPR_fact[] PROGMEM = "fact";
//#define _OPR_OOX_KW             215
const char _OPR_CNK[] PROGMEM = "CNK";
const char _OPR_cnk[] PROGMEM = "cnk";
//#define _OPR_K2C_KW             216
const char _OPR_K2C[] PROGMEM = "K2C";
const char _OPR_k2c[] PROGMEM = "k2c";
//#define _OPR_AIN_KW             217
const char _OPR_AIN[] PROGMEM = "AIN";
const char _OPR_ain[] PROGMEM = "ain";
//#define _OPR_KM2MI_KW           218
const char _OPR_KM2MI[] PROGMEM = "KM2MI";
const char _OPR_km2mi[] PROGMEM = "km2mi";
//#define _OPR_MI2KM_KW           219
const char _OPR_MI2KM[] PROGMEM = "KM2MI";
const char _OPR_mi2km[] PROGMEM = "mi2km";
//#define _OPR_IN2MM_KW           220
const char _OPR_IN2MM[] PROGMEM = "IN2MM";
const char _OPR_in2mm[] PROGMEM = "in2mm";
//#define _OPR_SFT2SM_KW          221
const char _OPR_SFT2SM[] PROGMEM = "SFT2SM";
const char _OPR_sft2sm[] PROGMEM = "sft2sm";
//#define _OPR_R2D_KW             222
const char _OPR_R2D[] PROGMEM = "R2D";
const char _OPR_r2d[] PROGMEM = "r2d";
//#define _OPR_D2R_KW             223
const char _OPR_D2R[] PROGMEM = "D2R";
const char _OPR_d2r[] PROGMEM = "d2r";
//#define _OPR_DELETE_KW          224
const char _OPR_DELETE[] PROGMEM = "DELETE";
const char _OPR_delete[] PROGMEM = "delete";
//#define _OPR_MOVE_KW            225
const char _OPR_MOVE[] PROGMEM = "MOVE";
const char _OPR_move[] PROGMEM = "move";
//#define _OPR_COPY_KW            226
const char _OPR_COPY[] PROGMEM = "COPY";
const char _OPR_copy[] PROGMEM = "copy";
//#define _OPR_TYPE_KW            227
const char _OPR_TYPE[] PROGMEM = "TYPE";
const char _OPR_type[] PROGMEM = "type";
//#define _OPR_INJECT_KW          228
const char _OPR_INJECT[] PROGMEM = "INJECT";
const char _OPR_inject[] PROGMEM = "inject";
//#define _OPR_MKDIR_KW           229
const char _OPR_MKDIR[] PROGMEM = "MKDIR";
const char _OPR_mkdir[] PROGMEM = "mkdir";


void Keywords::init(){
  _addKeyword( _OPR_ABS, _OPR_abs);                    // 0
  _addKeyword( _OPR_ACOS, _OPR_acos);                  // 1
  _addKeyword( _OPR_ACOSH, _OPR_acosh);                // 2
  _addKeyword( _OPR_ADD, _OPR_add);                    // 3
  _addKeyword( _OPR_AMODE, _OPR_amode);                // 4
  _addKeyword( _OPR_API2GCC, _OPR_api2gcc);            // 5
  _addKeyword( _OPR_APPEND, _OPR_append);              // 6
  _addKeyword( _OPR_AREAD, _OPR_aread);                // 7
  _addKeyword( _OPR_AREAD_INT, _OPR_aread_INT);        // 8
  _addKeyword( _OPR_ASC, _OPR_asc);                    // 9
  _addKeyword( _OPR_ASIN, _OPR_asin);                  // 10
  _addKeyword( _OPR_ASINH, _OPR_asinh);                // 11
  _addKeyword( _OPR_AT, _OPR_at);                      // 12
  _addKeyword( _OPR_ATAN, _OPR_atan);                  // 13
  _addKeyword( _OPR_ATANH, _OPR_atanh);                // 14
  _addKeyword( _OPR_AWRITE, _OPR_awrite);              // 15
  _addKeyword( _OPR_AZIMUTH, _OPR_azimuth);            // 16
  _addKeyword( _OPR_AZIMUTH3, _OPR_azimuth3);          // 17
  _addKeyword( _OPR_BAR2PSI, _OPR_bar2psi);            // 18
  _addKeyword( _OPR_BBL2CM, _OPR_bbl2cm);              // 19
  _addKeyword( _OPR_BREAK, _OPR_break);                // 20
  _addKeyword( _OPR_C2F, _OPR_c2f);                    // 21
  _addKeyword( _OPR_C2K, _OPR_c2k);                    // 22
  _addKeyword( _OPR_CATH, _OPR_cath);                  // 23
  _addKeyword( _OPR_CF2CM, _OPR_cf2cm);                // 24
  _addKeyword( _OPR_CHAIN, _OPR_chain);                // 25
  _addKeyword( _OPR_CHR_STR, _OPR_chr_STR);            // 26
  _addKeyword( _OPR_CIRCLE, _OPR_circle);              // 27
  _addKeyword( _OPR_CLEAR, _OPR_clear);                // 28
  _addKeyword( _OPR_CLI, _OPR_cli);                    // 29
  _addKeyword( _OPR_CLOSE, _OPR_close);                // 30
  _addKeyword( _OPR_CLS, _OPR_cls);                    // 31
  _addKeyword( _OPR_CM2BBL, _OPR_cm2bbl);              // 32
  _addKeyword( _OPR_CM2CF, _OPR_cm2cf);                // 33
  _addKeyword( _OPR_COLOR, _OPR_color);                // 34
  _addKeyword( _OPR_CON, _OPR_con);                    // 35
  _addKeyword( _OPR_CONST, _OPR_const);                // 36
  _addKeyword( _OPR_CONT, _OPR_cont);                  // 37
  _addKeyword( _OPR_CONTINUE, _OPR_continue);          // 38
  _addKeyword( _OPR_COORDS, _OPR_coords);              // 39
  _addKeyword( _OPR_COORDS3, _OPR_coords3);            // 40
  _addKeyword( _OPR_COS, _OPR_cos);                    // 41
  _addKeyword( _OPR_COSH, _OPR_cosh);                  // 42
  _addKeyword( _OPR_COT, _OPR_cot);                    // 43
  _addKeyword( _OPR_CURSOR, _OPR_cursor);              // 44
  _addKeyword( _OPR_D2DMS, _OPR_d2dms);                // 45
  _addKeyword( _OPR_DATA, _OPR_data);                  // 46
  _addKeyword( _OPR_DEF, _OPR_def);                    // 47
  _addKeyword( _OPR_DELAY, _OPR_delay);                // 48
  _addKeyword( _OPR_DET, _OPR_det);                    // 49
  _addKeyword( _OPR_DIM, _OPR_dim);                    // 50
  _addKeyword( _OPR_DIR, _OPR_dir);                    // 51
  _addKeyword( _OPR_DIRECTORY, _OPR_directory);        // 52
  _addKeyword( _OPR_DIV, _OPR_div);                    // 53
  _addKeyword( _OPR_DMODE, _OPR_dmode);                // 54
  _addKeyword( _OPR_DMS2D, _OPR_dms2d);                // 55
  _addKeyword( _OPR_DNOTONE, _OPR_dnotone);            // 56
  _addKeyword( _OPR_DOT, _OPR_dot);                    // 57
  _addKeyword( _OPR_DREAD, _OPR_dread);                // 58
  _addKeyword( _OPR_DTONE, _OPR_dtone);                // 59
  _addKeyword( _OPR_DUMP, _OPR_dump);                  // 60
  _addKeyword( _OPR_DWRITE, _OPR_dwrite);              // 61
  _addKeyword( _OPR_EDIT, _OPR_edit);                  // 62
  _addKeyword( _OPR_ELLIPSE, _OPR_ellipse);            // 63
  _addKeyword( _OPR_ELSE, _OPR_else);                  // 64
  _addKeyword( _OPR_END, _OPR_end);                    // 65
  _addKeyword( _OPR_ENDIF, _OPR_endif);                // 66
  _addKeyword( _OPR_ENDLOOP, _OPR_endloop);            // 67
  _addKeyword( _OPR_EXP, _OPR_exp);                    // 68
  _addKeyword( _OPR_F2C, _OPR_f2c);                    // 69
  _addKeyword( _OPR_FLOAT, _OPR_float);                // 70
  _addKeyword( _OPR_FMAN, _OPR_fman);                  // 71
  _addKeyword( _OPR_FN, _OPR_fn);                      // 72
  _addKeyword( _OPR_FOR, _OPR_for);                    // 73
  _addKeyword( _OPR_FREAD, _OPR_fread);                // 74
  _addKeyword( _OPR_FREAD_STR, _OPR_fread_STR);        // 75
  _addKeyword( _OPR_FSIZE, _OPR_fsize);                // 76
  _addKeyword( _OPR_FT2M, _OPR_ft2m);                  // 77
  _addKeyword( _OPR_GAL2L, _OPR_gal2l);                // 78
  _addKeyword( _OPR_GCC2API, _OPR_gcc2api);            // 79
  _addKeyword( _OPR_GOFF2, _OPR_goff2);                // 80
  _addKeyword( _OPR_GOSUB, _OPR_gosub);                // 81
  _addKeyword( _OPR_GOTO, _OPR_goto);                  // 82
  _addKeyword( _OPR_HEX_STR, _OPR_hex_STR);            // 83
  _addKeyword( _OPR_IDN, _OPR_idn);                    // 84
  _addKeyword( _OPR_IF, _OPR_if);                      // 85
  _addKeyword( _OPR_INCH16_STR, _OPR_inch16_STR);      // 86
  _addKeyword( _OPR_INCH2_STR, _OPR_inch2_STR);        // 87
  _addKeyword( _OPR_INCH32_STR, _OPR_inch32_STR);      // 88
  _addKeyword( _OPR_INCH32_STR, _OPR_inch32_STR);      // 89
  _addKeyword( _OPR_INCH4_STR, _OPR_inch4_STR);        // 90
  _addKeyword( _OPR_INCH8_STR, _OPR_inch8_STR);        // 91
  _addKeyword( _OPR_INJ, _OPR_inj);                    // 92
  _addKeyword( _OPR_INKEY_STR, _OPR_inkey_STR);        // 93
  _addKeyword( _OPR_INPUT, _OPR_input);                // 94
  _addKeyword( _OPR_INSCAN_STR, _OPR_inscan_STR);      // 95
  _addKeyword( _OPR_INT_INT, _OPR_int_INT);            // 96
  _addKeyword( _OPR_INV, _OPR_inv);                    // 97
  _addKeyword( _OPR_KG2LBS, _OPR_kg2lbs);              // 98
  _addKeyword( _OPR_KM2M, _OPR_km2m);                  // 99
  _addKeyword( _OPR_KM2NM, _OPR_km2nm);                // 100
  _addKeyword( _OPR_KMH2MS, _OPR_kmh2ms);              // 101
  _addKeyword( _OPR_L2GAL, _OPR_l2gal);                // 102
  _addKeyword( _OPR_LBS2KG, _OPR_lbs2kg);              // 103
  _addKeyword( _OPR_LCIRC, _OPR_lcirc);                // 104
  _addKeyword( _OPR_LEFT_STR, _OPR_left_STR);          // 105
  _addKeyword( _OPR_LET, _OPR_let);                    // 106
  _addKeyword( _OPR_LG, _OPR_lg);                      // 107
  _addKeyword( _OPR_LIN2, _OPR_lin2);                  // 108
  _addKeyword( _OPR_LINE, _OPR_line);                  // 109
  _addKeyword( _OPR_LINETO, _OPR_lineto);              // 110
  _addKeyword( _OPR_LINEW, _OPR_linew);                // 111
  _addKeyword( _OPR_LIST, _OPR_list);                  // 112
  _addKeyword( _OPR_LN, _OPR_ln);                      // 113
  _addKeyword( _OPR_LOAD, _OPR_load);                  // 114
  _addKeyword( _OPR_LOG, _OPR_log);                    // 115
  _addKeyword( _OPR_LOOP, _OPR_loop);                  // 116
  _addKeyword( _OPR_LT2MT, _OPR_lt2mt);                // 117
  _addKeyword( _OPR_M2FT, _OPR_m2ft);                  // 118
  _addKeyword( _OPR_M2KM, _OPR_m2km);                  // 119
  _addKeyword( _OPR_MAT, _OPR_mat);                    // 120
  _addKeyword( _OPR_MATRIX, _OPR_matrix);              // 121
  _addKeyword( _OPR_MEM, _OPR_mem);                    // 122
  _addKeyword( _OPR_MID_STR, _OPR_mid_STR);            // 123
  _addKeyword( _OPR_MM2IN, _OPR_mm2in);                // 124
  _addKeyword( _OPR_MOD, _OPR_mod);                    // 125
  _addKeyword( _OPR_MPA2PSI, _OPR_mpa2psi);            // 126
  _addKeyword( _OPR_MS2KMH, _OPR_ms2kmh);              // 127
  _addKeyword( _OPR_MT2LT, _OPR_mt2lt);                // 128
  _addKeyword( _OPR_MT2ST, _OPR_mt2st);                // 129
  _addKeyword( _OPR_MUL, _OPR_mul);                    // 130
  _addKeyword( _OPR_NDIS, _OPR_ndis);                  // 131
  _addKeyword( _OPR_NEG, _OPR_neg);                    // 132
  _addKeyword( _OPR_NEW, _OPR_new);                    // 133
  _addKeyword( _OPR_NEXT, _OPR_next);                  // 134
  _addKeyword( _OPR_NM2KM, _OPR_nm2km);                // 135
  _addKeyword( _OPR_OPEN, _OPR_open);                  // 136
  _addKeyword( _OPR_PA2PSI, _OPR_pa2psi);              // 137
  _addKeyword( _OPR_PAUSE, _OPR_pause);                // 138
  _addKeyword( _OPR_POINT, _OPR_point);                // 139
  _addKeyword( _OPR_POKE, _OPR_poke);                  // 140
  _addKeyword( _OPR_POP, _OPR_pop);                    // 141
  _addKeyword( _OPR_POW, _OPR_pow);                    // 142
  _addKeyword( _OPR_PRINT, _OPR_print);                // 143
  _addKeyword( _OPR_PRINTALT, _OPR_printalt);          // 144
  _addKeyword( _OPR_PROB, _OPR_prob);                  // 145
  _addKeyword( _OPR_PROBIT, _OPR_probit);              // 146
  _addKeyword( _OPR_PROBR, _OPR_probr);                // 147
  _addKeyword( _OPR_PROGRAM, _OPR_program);            // 148
  _addKeyword( _OPR_PSI2BAR, _OPR_psi2bar);            // 149
  _addKeyword( _OPR_PSI2MPA, _OPR_psi2mpa);            // 150
  _addKeyword( _OPR_PSI2PA, _OPR_psi2pa);              // 151
  _addKeyword( _OPR_PSIA2PSIG, _OPR_psia2psig);        // 152
  _addKeyword( _OPR_PSIG2PSIA, _OPR_psig2psia);        // 153
  _addKeyword( _OPR_PUSH, _OPR_push);                  // 154
  _addKeyword( _OPR_QUAD, _OPR_quad);                  // 155
  _addKeyword( _OPR_RADIUS, _OPR_radius);              // 156
  _addKeyword( _OPR_RANDOM, _OPR_random);              // 157
  _addKeyword( _OPR_RANDOM_INT, _OPR_random_INT);      // 158
  _addKeyword( _OPR_READ, _OPR_read);                  // 159
  _addKeyword( _OPR_RECT, _OPR_rect);                  // 160
  _addKeyword( _OPR_REGR, _OPR_regr);                  // 161
  _addKeyword( _OPR_REM, _OPR_rem);                    // 162
  _addKeyword( _OPR_REMALT, _OPR_remalt);              // 163
  _addKeyword( _OPR_RESET, _OPR_reset);                // 164
  _addKeyword( _OPR_RESTORE, _OPR_restore);            // 165
  _addKeyword( _OPR_RIGHT_STR, _OPR_right_STR);        // 166
  _addKeyword( _OPR_RMD, _OPR_rmd);                    // 167
  _addKeyword( _OPR_RND, _OPR_rnd);                    // 168
  _addKeyword( _OPR_ROOT, _OPR_root);                  // 169
  _addKeyword( _OPR_ROT, _OPR_rot);                    // 170
  _addKeyword( _OPR_ROT3c, _OPR_rot3c);                // 171
  _addKeyword( _OPR_ROT3s, _OPR_rot3s);                // 172
  _addKeyword( _OPR_ROUND, _OPR_round);                // 173
  _addKeyword( _OPR_RPN, _OPR_rpn);                    // 174
  _addKeyword( _OPR_RUN, _OPR_run);                    // 175
  _addKeyword( _OPR_SAVE, _OPR_save);                  // 176
  _addKeyword( _OPR_SCIRC, _OPR_scirc);                // 177
  _addKeyword( _OPR_SCREEN, _OPR_screen);              // 178
  _addKeyword( _OPR_SEED, _OPR_seed);                  // 179
  _addKeyword( _OPR_SIGN, _OPR_sign);                  // 180
  _addKeyword( _OPR_SIN, _OPR_sin);                    // 181
  _addKeyword( _OPR_SINH, _OPR_sinh);                  // 182
  _addKeyword( _OPR_SM2SFT, _OPR_sm2sft);              // 183
  _addKeyword( _OPR_SQ, _OPR_sq);                      // 184
  _addKeyword( _OPR_SQRT, _OPR_sqrt);                  // 185
  _addKeyword( _OPR_SSPHERE, _OPR_ssphere);            // 186
  _addKeyword( _OPR_ST2MT, _OPR_st2mt);                // 187
  _addKeyword( _OPR_STACK, _OPR_stack);                // 188
  _addKeyword( _OPR_STAT, _OPR_stat);                  // 189
  _addKeyword( _OPR_STATXY, _OPR_statxy);              // 190
  _addKeyword( _OPR_STEP, _OPR_step);                  // 191
  _addKeyword( _OPR_STOP, _OPR_stop);                  // 192
  _addKeyword( _OPR_STORE, _OPR_store);                // 193
  _addKeyword( _OPR_STR_STR, _OPR_str_STR);            // 194
  _addKeyword( _OPR_SUB, _OPR_sub);                    // 195
  _addKeyword( _OPR_SUM, _OPR_sum);                    // 196
  _addKeyword( _OPR_SUMS, _OPR_sums);                  // 197
  _addKeyword( _OPR_SUMXY, _OPR_sumxy);                // 198
  _addKeyword( _OPR_SWAP, _OPR_swap);                  // 199
  _addKeyword( _OPR_TAN, _OPR_tan);                    // 200
  _addKeyword( _OPR_TANH, _OPR_tanh);                  // 201
  _addKeyword( _OPR_TERM, _OPR_term);                  // 202
  _addKeyword( _OPR_TIME, _OPR_time);                  // 203
  _addKeyword( _OPR_TO, _OPR_to);                      // 204
  _addKeyword( _OPR_TRN, _OPR_trn);                    // 205
  _addKeyword( _OPR_VARS, _OPR_vars);                  // 206
  _addKeyword( _OPR_VECTOR, _OPR_vector);              // 207
  _addKeyword( _OPR_VSPHERE, _OPR_vsphere);            // 208
  _addKeyword( _OPR_WEEKDAY, _OPR_weekday);            // 209
  _addKeyword( _OPR_WRITE, _OPR_write);                // 210
  _addKeyword( _OPR_ZER, _OPR_zer);                    // 211
  _addKeyword( _OPR_ROLL, _OPR_roll);                  // 212
  _addKeyword( _OPR_OOX, _OPR_oox);                    // 213
  _addKeyword( _OPR_FACT, _OPR_fact);                  // 214
  _addKeyword( _OPR_CNK, _OPR_cnk);                    // 215
  _addKeyword( _OPR_K2C, _OPR_k2c);                    // 216
  _addKeyword( _OPR_AIN, _OPR_ain);                    // 217
  _addKeyword( _OPR_KM2MI, _OPR_km2mi);                // 218
  _addKeyword( _OPR_MI2KM, _OPR_mi2km);                // 219
  _addKeyword( _OPR_IN2MM, _OPR_in2mm);                // 220
  _addKeyword( _OPR_SFT2SM, _OPR_sft2sm);              // 221
  _addKeyword( _OPR_R2D, _OPR_r2d);                    // 222
  _addKeyword( _OPR_D2R, _OPR_d2r);                    // 223
  _addKeyword( _OPR_DELETE, _OPR_delete);              // 224
  _addKeyword( _OPR_MOVE, _OPR_move);                  // 225
  _addKeyword( _OPR_COPY, _OPR_copy);                  // 226
  _addKeyword( _OPR_TYPE, _OPR_type);                  // 227
  _addKeyword( _OPR_INJECT, _OPR_inject);              // 228
  _addKeyword( _OPR_MKDIR, _OPR_mkdir);                // 229
  //_addKeyword( Add here, Add here);                  // 230
};

Keyword *Keywords::getKeyword(byte *str){
  for(size_t i=0; i<_OPERATOR_COUNT; i++){
    lastKeywordFound  = _keywords + i;
    if( IsKeyword(str, lastKeywordFound->name1)) return lastKeywordFound;
    if( IsKeyword(str, lastKeywordFound->name0)) return lastKeywordFound;
  }
  lastKeywordFound = NULL;
  return NULL; // not found
}

bool Keywords::isKeyword(byte *str){
  Keyword *tmp = _keywords;
  for(size_t i=0; i<_OPERATOR_COUNT; i++, tmp++){
    if( IsKeyword(str, tmp->name1)) return true;
    if( IsKeyword(str, tmp->name0)) return true;
  }
  return false; // not found
}

byte *Keywords::parse( byte *str){
  lastKeywordFound = NULL;
  byte tmp;
  byte *ptr = str;

  // skip empty space
  while( IsSpacer(*ptr)) ptr++;
  if( !IsNameStarter(*ptr)) return ptr;
  str = ptr;

  while( IsNameCharacter(*ptr)){
    // dollar or percent must be the last character
    if( *ptr == _DOLLAR_ || *ptr == _PERCENT_){
      ptr++;
      break;
    }
    ptr++;
  }
  tmp = *ptr; // preserve symbol
  *ptr = _NUL_;
  if( getKeyword(str) != NULL) str = ptr;
  *ptr = tmp; // restore symbol
  return str;
}

void Keywords::_addKeyword( const char *name0, const char *name1, void *method){
  if( _id >= _OPERATOR_COUNT) return;
  Keyword *tmp = _keywords + _id;
  tmp->id = _id++;
  tmp->name0 = name0;
  tmp->name1 = name1;
  tmp->operator_ptr = method;
  #ifdef __DEBUG
  Serial.print( tmp->id+1);
  Serial.print(" added operator keyword ");
  Serial.print( tmp->name0);
  Serial.print(", AKA ");
  Serial.print( tmp->name1);
  Serial.println( ".");
  #endif
}
