ptravnik/Retro_CALC/RetroRPN_ESP32/src/CP1251_font.h

//////////////////////////////////////////////////////////
//
//  RetroRPN - "Электроника МК-90" reborn
//  Copyright (c) 2019 Pavel Travnik.  All rights reserved.
//  See main file for the license
//
//////////////////////////////////////////////////////////

//
// 6x8 CP1251 font (see Font_Generator_CP1251.py)
//
const uint8_t CP1251_font[] PROGMEM = {
  0x00, 0x00, 0x00, 0x00, 0x00, 0x00, 0x00, 0x00, // 000 NUL
  0x70, 0xF8, 0xA8, 0xF8, 0xD8, 0x88, 0x70, 0x00, // 001 SOH
  0x70, 0xF8, 0xA8, 0xF8, 0x88, 0xD8, 0x70, 0x00, // 002 STX
  0x00, 0x50, 0xF8, 0xF8, 0xF8, 0x70, 0x20, 0x00, // 003 ETX
  0x00, 0x20, 0x70, 0xF8, 0xF8, 0x70, 0x20, 0x00, // 004 EOT
  0x70, 0x50, 0xF8, 0xA8, 0xF8, 0x20, 0x70, 0x00, // 005 ENQ
  0x20, 0x70, 0xF8, 0xF8, 0xF8, 0x20, 0x70, 0x00, // 006 ACK
  0x00, 0x00, 0x20, 0x70, 0x70, 0x20, 0x00, 0x00, // 007 BEL
  0xF8, 0xF8, 0xD8, 0x88, 0x88, 0xD8, 0xF8, 0xF8, // 008 BS
  0x00, 0x00, 0x20, 0x50, 0x50, 0x20, 0x00, 0x00, // 009 HT
  0xF8, 0xF8, 0xD8, 0xA8, 0xA8, 0xD8, 0xF8, 0xF8, // 010 LF
  0x00, 0x38, 0x18, 0x68, 0xA0, 0xA0, 0x40, 0x00, // 011 VT
  0x70, 0x88, 0x88, 0x70, 0x20, 0xF8, 0x20, 0x00, // 012 FF
  0x78, 0x48, 0x78, 0x40, 0x40, 0x40, 0xC0, 0x00, // 013 CR
  0x78, 0x48, 0x78, 0x48, 0x48, 0x58, 0xC0, 0x00, // 014 SO
  0x20, 0xA8, 0x70, 0xD8, 0xD8, 0x70, 0xA8, 0x20, // 015 SI
  0x80, 0xC0, 0xF0, 0xF8, 0xF0, 0xC0, 0x80, 0x00, // 016 DLE
  0x08, 0x18, 0x78, 0xF8, 0x78, 0x18, 0x08, 0x00, // 017 DC1 (LEFT)
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
  0x30, 0x50, 0x50, 0x50, 0x50, 0x50, 0xF8, 0x88, // 196
  0xF0, 0x80, 0x80, 0xE0, 0x80, 0x80, 0xF8, 0x00, // 197
  0xA8, 0x70, 0x20, 0x70, 0xA8, 0xA8, 0xA8, 0x00, // 198
  0x70, 0x88, 0x30, 0x08, 0x08, 0x88, 0x70, 0x00, // 199
  0x88, 0x88, 0x88, 0x98, 0xA8, 0xC8, 0x88, 0x00, // 200
  0x30, 0x88, 0x88, 0x98, 0xA8, 0xC8, 0x88, 0x00, // 201
  0x88, 0x90, 0xA0, 0xE0, 0x90, 0x88, 0x88, 0x00, // 202
  0x18, 0x28, 0x48, 0x88, 0x88, 0x88, 0x88, 0x00, // 203
  0x88, 0xD8, 0xA8, 0xA8, 0x88, 0x88, 0x88, 0x00, // 204
  0x88, 0x88, 0x88, 0xF8, 0x88, 0x88, 0x88, 0x00, // 205
  0x70, 0x88, 0x88, 0x88, 0x88, 0x88, 0x70, 0x00, // 206
  0xF8, 0x88, 0x88, 0x88, 0x88, 0x88, 0x88, 0x00, // 207
  0xF0, 0x88, 0x88, 0x88, 0xF0, 0x80, 0x80, 0x00, // 208
  0x70, 0x88, 0x80, 0x80, 0x80, 0x88, 0x70, 0x00, // 209
  0xF8, 0x20, 0x20, 0x20, 0x20, 0x20, 0x20, 0x00, // 210
  0x88, 0x88, 0x88, 0x78, 0x08, 0x08, 0x70, 0x00, // 211
  0x70, 0xA8, 0xA8, 0xA8, 0xA8, 0xA8, 0xF8, 0x20, // 212
  0x88, 0x88, 0x50, 0x20, 0x50, 0x88, 0x88, 0x00, // 213
  0x90, 0x90, 0x90, 0x90, 0x90, 0x90, 0xF8, 0x08, // 214
  0x88, 0x88, 0x88, 0x88, 0x78, 0x08, 0x08, 0x00, // 215
  0x88, 0x88, 0xA8, 0xA8, 0xA8, 0xA8, 0xF8, 0x00, // 216
  0x88, 0x88, 0x88, 0xA8, 0xA8, 0xA0, 0xF8, 0x08, // 217
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
};
