ptravnik/Retro_CALC/RetroRPN_ESP32/src/LCDManager.hpp

//////////////////////////////////////////////////////////
//
//  RetroRPN - "Электроника МК-90" reborn
//  Copyright (c) 2019 Pavel Travnik.  All rights reserved.
//  See main file for the license
//
//////////////////////////////////////////////////////////

//
// Pin assignment:
//
// 12 - LCD Data (R/W)
// 13 - LCD Reset (RESET)
// 14 - LCD Clock (E)
// 15 - LCD CS (RS)
// 16 - LCD POWER (this model does not have sleep)
// 17 - LCD LED PWM
//

// 12 - HSPI MISO LCD Data (R/W)
// 13 - HSPI MOSI LCD Reset (RESET)
// 14 - HSPI CLK LCD Clock (E)
// 15 - HSPI CSO LCD Select (RS)
// 21 - LCD LED PWM
// 22 - LCD POWER (this model does not have sleep)

#ifndef LCDMANAGER_HPP
#define LCDMANAGER_HPP

#include "IOManager.hpp"
#include "Variables.hpp"

// fade LED PIN (replace with LED_BUILTIN=2 constant for built-in LED)
// LCD PIN controls power for LCD
#define LCD_DATA           12
#define LCD_RESET          13
#define LCD_CLOCK          14
#define LCD_CS             15
#define LCD_POWER_PIN      22
#define LCD_LED_PIN        21

// use first channel of 16 channels (started from zero)
// use 13 bit precision for LEDC timer
// use 5000 Hz as a LEDC base frequency
#define LCD_LEDC_CHANNEL_0     0
#define LCD_LEDC_TIMER_13_BIT  13
#define LCD_LEDC_MAX_DUTY      8191
#define LCD_LEDC_BASE_FREQ     5000

// must be less than IO_BUFFER_LENGTH (256)
#define SCR_MAX_UTF (SCR_COLS + SCR_COLS + 1)
#define SCR_BUFFER_SIZE 1024

// cursor blinker rate in ms
#define BLINKER_RATE 500

// show splashscreen in ms
#define SCR_SPLASH  1000 

class LCDManager{
  public:
    bool isAsleep = false;
    bool isLEDoff = false;
    bool cursorShown = true;
    bool wordWrap = false;
    bool scrollLock = false;
    bool lineRedrawRequired[ SCR_ROWS];
    bool lineInversed[ SCR_ROWS];
    bool forceRedraw = false;
    byte ledBrightness = 200;

    unsigned long init( void *components[]);
    void waitForEndSplash( unsigned long start, bool cls = false);
    unsigned long tick();

    inline void setRedrawAll(bool r){
      memset( lineRedrawRequired, r, SCR_ROWS);
    }
    void redraw();
    
    void clearScreen( byte ch=_SP_, bool clear_inversed=false);
    void clearLine( byte row, byte ch=_SP_);
    void clearToEOL(byte ch=_SP_);
    void scrollUp( byte rows);
    void scrollDown( byte rows);
    
    void sendChar( byte c);
    void sendString( const byte *c, size_t limit=0);
    inline void sendString( const char *c, size_t limit=0){
      sendString( (const byte *)c, limit);
    };
    void sendStringUTF8( const char *c);
    inline void cursorToTop(){
      cursorTo( 0, 0);        
    };
    inline void cursorToBottom(){
      cursorTo( 0, SCR_BOTTOM);        
    };
    void cursorRight();
    void cursorLeft();
    void cursorUp();
    void cursorDown();
    void cursorTo( byte column, byte row);
    void sendCarriageReturn();   
    void sendTab();   
    void sendDelete();   
    void sendBackspace();
    void invertRow( byte row, bool invert);
    inline byte *getTextBuffer(){
      return _buffer;
      };  
    
    void setLED( byte v);
    void changeLED( int16_t v);
    
    uint8_t plotCharacter( uint8_t left, uint8_t top, uint8_t ch);
    uint8_t plotString( uint8_t left, uint8_t top, byte *str, byte limit=SCR_COLS);
    inline uint8_t plotString( uint8_t left, uint8_t top, char *str, byte limit=SCR_COLS){
      plotString( left, top, (byte *)str, limit);
    };
    uint8_t plotStringUTF8( uint8_t left, uint8_t top, const char *str);

    void sleepOn();
    void sleepOff();
    void LEDOn();
    void LEDOff();
    inline unsigned long keepAwake(){
      return _iom->keepAwake();
    };

  private:
    byte *_io_buffer;
    IOManager *_iom;
    Variables *_vars;
    bool _blinked = false;
    uint32_t _last_blinked = 0;
    uint16_t _cursor_column = 0;
    uint16_t _cursor_row = 0;
    inline size_t _cursor_position(){
      return _cursor_row * SCR_COLS + _cursor_column;
      };
    byte _buffer[SCR_SIZE];
    uint8_t _tileHeight = 0;
    uint8_t _tileWidth = 0;
    uint8_t *_graphics;
    int64_t *_ledPWM = NULL;
    void _dimLED( byte start_duty, byte stop_duty, byte step=30);
    void _ledcAnalogWrite(uint8_t channel, uint8_t value);
};

#endif // LCDMANAGER_HPP
