ptravnik/Retro_CALC/HWKbd/src/Cyrillic_Phonetic.h

/*
  Cyrillic_Phonetic.h - codes and macros for Hardware keyboard.
  Copyright (c) 2019 Pavel Travnik.  All rights reserved.

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
  You should have received a copy of the GNU Lesser General Public
  License along with this library; if not, write to the Free Software
  Foundation, Inc., 51 Franklin St, Fifth Floor, Boston, MA  02110-1301  USA
*/

const static uint16_t HWKBD_Codepage_Cyrillic_Phonetic_UTF8[] PROGMEM = {
0x0000,0x0000,0x0000,0x0000,0x4000,0x4000,0x4000,0x4000, // Button 01
0x0000,0x0000,0x0000,0x0000,0x4000,0x4000,0x4000,0x4000, // Button 02
0x0000,0x0000,0x0000,0x0000,0x4000,0x4000,0x4000,0x4000, // Button 03
0x0000,0x0000,0x0000,0x0000,0x4000,0x4000,0x4000,0x4000, // Button 04
0x0000,0x0000,0x0000,0x0000,0x4000,0x4000,0x4000,0x4000, // Button 05
0x0000,0x0000,0x0000,0x0000,0x4000,0x4000,0x4000,0x4000, // Button 06
0x002b,0x0026,0x0000,0x0000,0x4000,0x4000,0x4000,0x4000, // Button 07
0x002d,0x007c,0x0000,0x0000,0x4000,0x4000,0x4000,0x4000, // Button 08
0x002a,0x005e,0x0000,0x0000,0x4000,0x4000,0x4000,0x4000, // Button 09
0x002f,0x0025,0x0000,0x0000,0x4000,0x4000,0x4000,0x4000, // Button 10
0x0031,0x0060,0x0000,0x0000,0xc000,0xc003,0x4000,0x4000, // Button 11
0x0032,0x0040,0x0000,0x0000,0xc006,0xc009,0x4000,0x4000, // Button 12
0x0033,0x007e,0x0000,0x0000,0xc00c,0xc00f,0x4000,0x4000, // Button 13
0x0034,0x8012,0x0000,0x0000,0xc015,0xc018,0x4000,0x4000, // Button 14
0x0035,0x801b,0x0000,0x0000,0xc01e,0xc021,0x4000,0x4000, // Button 15
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
0x67,0x68,0x74,0x00,0x53,0x2d,0x72,0x69,0x67,0x68,0x74,0x00,0x65,0x6e,0x64,0x00,
0x53,0x2d,0x65,0x6e,0x64,0x00,0x53,0x43,0x2d,0x65,0x6e,0x64,0x00,0x53,0x43,0x2d,
0x68,0x6f,0x6d,0x65,0x00,0x53,0x43,0x2d,0x65,0x6e,0x64,0x00,0x53,0x43,0x2d,0x68,
0x6f,0x6d,0x65,0x00
};
