ptravnik/Retro_CALC/HWKbd/src/Morse_Code.h

/*
  Morse_Code.h - International Morse code for Hardware keyboard.
  Copyright (c) 2019 Pavel Travnik.  All rights reserved.

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
  You should have received a copy of the GNU Lesser General Public
  License along with this library; if not, write to the Free Software
  Foundation, Inc., 51 Franklin St, Fifth Floor, Boston, MA  02110-1301  USA
*/


const static uint16_t HWKBD_Codepage_IMC[] PROGMEM = {
0x8000,0x0000,0x0000,0x0000,0x4000,0x4000,0x4000,0x4000, // Button 01
0x0000,0x0000,0x0000,0x0000,0x4000,0x4000,0x4000,0x4000, // Button 02
0x0000,0x0000,0x0000,0x0000,0x4000,0x4000,0x4000,0x4000, // Button 03
0x0000,0x0000,0x0000,0x0000,0x4000,0x4000,0x4000,0x4000, // Button 04
0x0000,0x0000,0x0000,0x0000,0x4000,0x4000,0x4000,0x4000, // Button 05
0x0000,0x0000,0x0000,0x0000,0x4000,0x4000,0x4000,0x4000, // Button 06
0x0000,0x0000,0x0000,0x0000,0x4000,0x4000,0x4000,0x4000, // Button 07
0x0000,0x0000,0x0000,0x0000,0x4000,0x4000,0x4000,0x4000, // Button 08
0x0000,0x0000,0x0000,0x0000,0x4000,0x4000,0x4000,0x4000, // Button 09
0x0000,0x0000,0x0000,0x0000,0x4000,0x4000,0x4000,0x4000, // Button 10
0x800f,0x0000,0x0000,0x0000,0x4000,0x4000,0x4000,0x4000, // Button 11
0x8018,0x0000,0x0000,0x0000,0x4000,0x4000,0x4000,0x4000, // Button 12
0x8021,0x0000,0x0000,0x0000,0x4000,0x4000,0x4000,0x4000, // Button 13
0x802a,0x0000,0x0000,0x0000,0x4000,0x4000,0x4000,0x4000, // Button 14
0x8033,0x0000,0x0000,0x0000,0x4000,0x4000,0x4000,0x4000, // Button 15
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
0x00,0x5f,0x73,0x70,0x61,0x63,0x65,0x20,0x20,0x20,0x00,0x5f,0x42,0x20,0x2d,0x2e,
0x2e,0x2e,0x00,0x5f,0x4e,0x20,0x2d,0x2e,0x00,0x5f,0x4d,0x20,0x2d,0x2d,0x00,0x5f,
0x64,0x6f,0x74,0x20,0x2d,0x2e,0x2e,0x20,0x2d,0x2d,0x2d,0x20,0x2d,0x00
};
