ptravnik/Retro_CALC/MK2090_Peripheral_Controller/src/Commander.hpp

//////////////////////////////////////////////////////////
//
//  RetroRPN - "Электроника МК-90" reborn
//  Copyright (c) 2020 Mike Yakimov.  All rights reserved.
//  See main file for the license
//
//////////////////////////////////////////////////////////

#ifndef COMMANDER_HPP
#define COMMANDER_HPP

#include <Arduino.h>
#include "CircularBuffer.hpp"

#define NCOMMANDS                 16
#define INPUT_BUFFER_LENGTH       40
#define COMMAND_SET_DATETIME      'A'
#define COMMAND_GET_DATETIME      'B'
#define COMMAND_GET_TEMPERATURE   'C'
#define COMMAND_GET_VOLTAGE       'D'
#define COMMAND_IS_SHUTDOWN       'E'
#define COMMAND_SHUTDOWN          'F'
#define COMMAND_SETWAKEUP         'G'
#define COMMAND_GETWAKEUP         'H'
#define COMMAND_SETLCDDUTYCYCLE   'I'
#define COMMAND_GETLCDDUTYCYCLE   'J'
#define COMMAND_PLAYTONE          'K'

struct Command{
    uint8_t code;
    void (*action)( char *, uint8_t);
};

class Commander{
  public:
    void begin( CircularBuffer *buffer);
    void addCommand( uint8_t code, void (*action)( char *, uint8_t));
    void read();
    char _inputBuff[INPUT_BUFFER_LENGTH];
  private:
    uint8_t _ncomm = 0;
    Command _commands[NCOMMANDS];
    CircularBuffer *_buffer;
};

#endif
