ptravnik/Retro_CALC/HWKbd/src/RPN_Calc_Encoding.h

/*
  RPN_Calculator.h - codes and macros for Hardware keyboard.
  Copyright (c) 2019 Pavel Travnik.  All rights reserved.

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
  You should have received a copy of the GNU Lesser General Public
  License along with this library; if not, write to the Free Software
  Foundation, Inc., 51 Franklin St, Fifth Floor, Boston, MA  02110-1301  USA
*/

const static uint16_t HWKBD_Codepage_RPN[] PROGMEM = {
0x0000,0x0000,0x0000,0x0000,0x4000,0x4000,0x4000,0x4000, // Button 01
0x0000,0x0000,0x0000,0x0000,0x4000,0x4000,0x4000,0x4000, // Button 02
0x0000,0x0000,0x0000,0x0000,0x4000,0x4000,0x4000,0x4000, // Button 03
0x0000,0x0000,0x0000,0x0000,0x4000,0x4000,0x4000,0x4000, // Button 04
0x0000,0x0000,0x0000,0x0000,0x4000,0x4000,0x4000,0x4000, // Button 05
0x0000,0x0000,0x0000,0x0000,0x4000,0x4000,0x4000,0x4000, // Button 06
0x002b,0x0000,0x0000,0x0000,0x4000,0x4000,0x4000,0x4000, // Button 07
0x002d,0x0000,0x0000,0x0000,0x4000,0x4000,0x4000,0x4000, // Button 08
0x002a,0x0000,0x0000,0x0000,0x4000,0x4000,0x4000,0x4000, // Button 09
0x002f,0x0025,0x0000,0x0000,0x4000,0x4000,0x4000,0x4000, // Button 10
0x0000,0x0000,0x0000,0x0000,0x4000,0x4000,0x4000,0x4000, // Button 11
0x0000,0x0000,0x0000,0x0000,0x4000,0x4000,0x4000,0x4000, // Button 12
0x0000,0x0000,0x0000,0x0000,0x4000,0x4000,0x4000,0x4000, // Button 13
0x0000,0x0000,0x0000,0x0000,0x4000,0x4000,0x4000,0x4000, // Button 14
0x0000,0x0000,0x0000,0x0000,0x4000,0x4000,0x4000,0x4000, // Button 15
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
0x1000,0x1000,0x1000,0x1000,0x5000,0x5000,0x5000,0x5000  // Button 59
};

const static byte HWKBD_Macropage_RPN[] PROGMEM = {
0x30,0x30,0x00,0x01,0xb1,0x00,0x01,0x06,0x00,0x01,0x08,0x00,0x01,0x01,0x00,0x01,
0x02,0x00,0x01,0x03,0x00,0x01,0x04,0x00,0x01,0x05,0x00
};
