ptravnik/Retro_CALC/MK2090_Peripheral_Controller/src/CircularBuffer.hpp

//////////////////////////////////////////////////////////
//
//  RetroRPN - "Электроника МК-90" reborn
//  Copyright (c) 2020 Mike Yakimov.  All rights reserved.
//  See main file for the license
//
//////////////////////////////////////////////////////////

#ifndef CIRCULAR_BUFFER_HPP
#define CIRCULAR_BUFFER_HPP

#include <Arduino.h>

#define CIRCULAR_BUFFER_LENGTH 256

class CircularBuffer{
  public:
    inline bool available(){
      return _in != _out;
      };
    void push( char c);
    char pop();
    char peek();
  private:
    size_t _in = 0;
    size_t _out = 0;
    char _buffer[CIRCULAR_BUFFER_LENGTH];
};

#endif
