ptravnik/Retro_CALC/RetroRPN_ESP32/src/operator_SUM.hpp

//////////////////////////////////////////////////////////
//
//  RetroRPN - "Электроника МК-90" reborn
//  Copyright (c) 2019 Pavel Travnik.  All rights reserved.
//  See main file for the license
//
//////////////////////////////////////////////////////////

// This include is for convenience of coding; comment out
//#include "Lexer.hpp"

//
// 1-D statistics
//
static bool _operator_SUM_( Lexer *lex){
  return lex->operator_SUM();
}
bool Lexer::operator_SUM(){
  #ifdef __DEBUG
  Serial.println("SUM called");
  Serial.print("Evaluating: |");
  Serial.println((char *)_lexer_position);
  #endif
  // parse expression
  byte nArgs = _parseList( 1);
  if( nArgs == 1){
    _vars->addSample2RPNSum( _listValues[0]);
  }
  else{
      _vars->saveRPNPrev();
      _vars->addSample2RPNSum( _vars->getRPNRegister());
      _vars->popRPNStack();
  }
  _vars->pushRPNStack( _vars->nmean[0]);
  _vars->pushRPNStack( _vars->stdev[0]);
  _vars->pushRPNStack( _vars->mean[0]);

  _vars->setRPNLabelZ( LEX_Message_N);
  _vars->setRPNLabelY( LEX_Message_stDev);
  _vars->setRPNLabelX( LEX_Message_Mean);
  _vars->setScrMessage( LEX_Message_SumUpdated);
  _mbox->setRedrawRequired();
  _rsb->setStackRedrawAll();
  _rsb->setLabelRedrawAll();
  _skipToNextOperator( _lexer_position);
  return true;
}
